knicholes/ah-my-groin-button/case/v1-200x130x110/preview-button-notch-detail.png

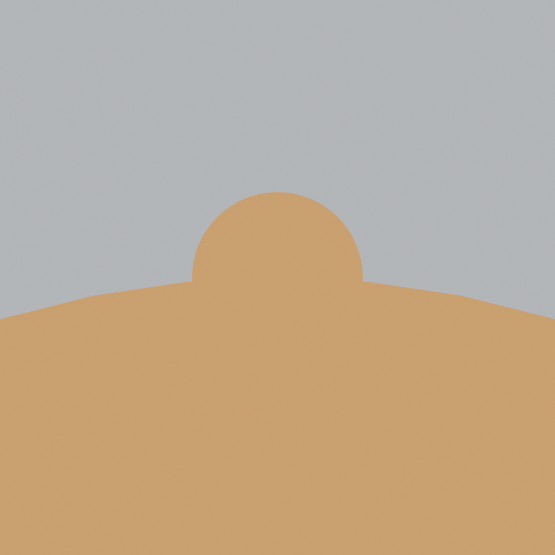
case/v1-200x130x110/preview-button-notch-detail.png
