knicholes/ah-my-groin-button/case/v1-200x130x110/preview-button-notches.png

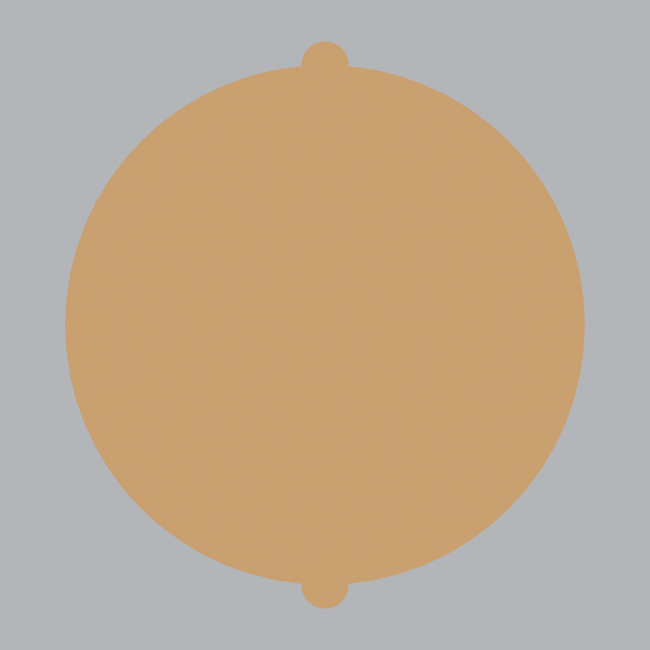
case/v1-200x130x110/preview-button-notches.png
