knicholes/ah-my-groin-button/case/v1-200x130x110/preview-tray-bottom.png

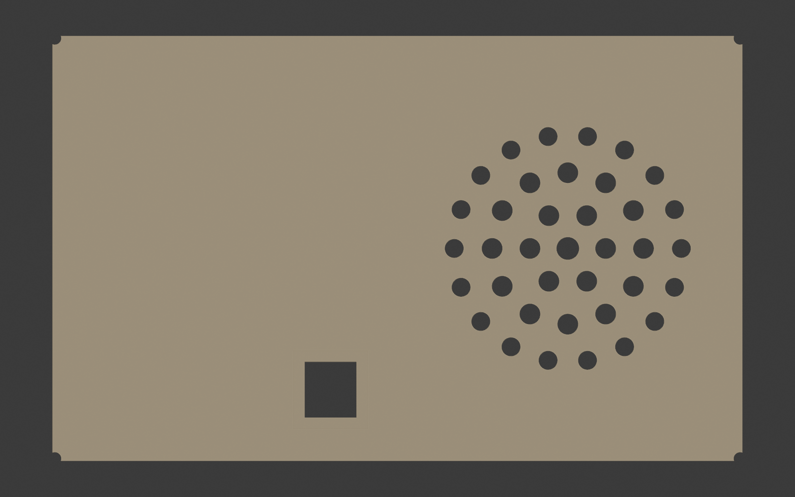
case/v1-200x130x110/preview-tray-bottom.png
