knicholes/ah-my-groin-button/case/v1-200x130x110/render-top.png

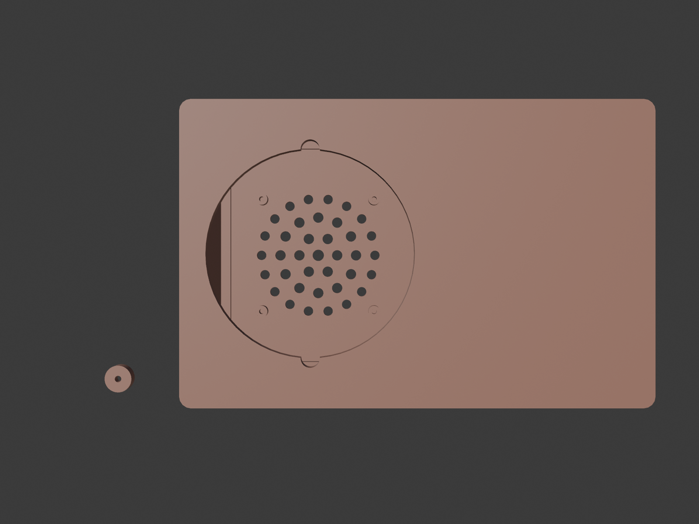
case/v1-200x130x110/render-top.png
