knicholes/ah-my-groin-button/case/v1-200x130x110/render-tray_top.png

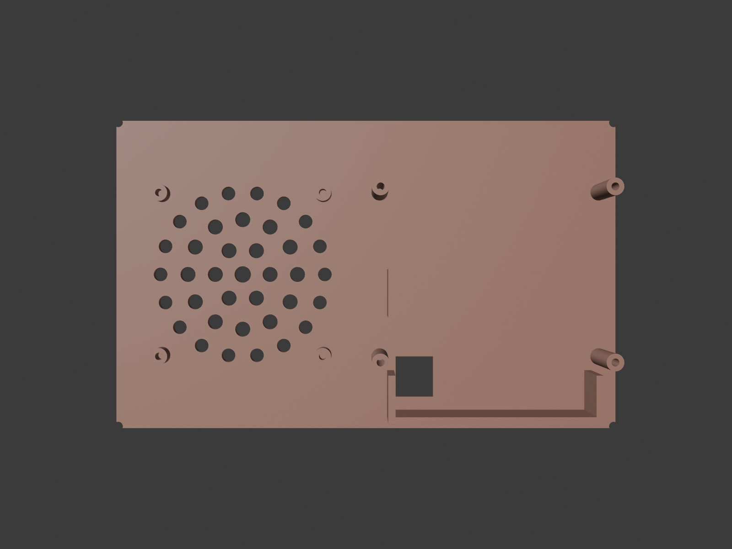
case/v1-200x130x110/render-tray_top.png
