knicholes/ah-my-groin-button/case/v2-120x120x140/preview-switch-window.png

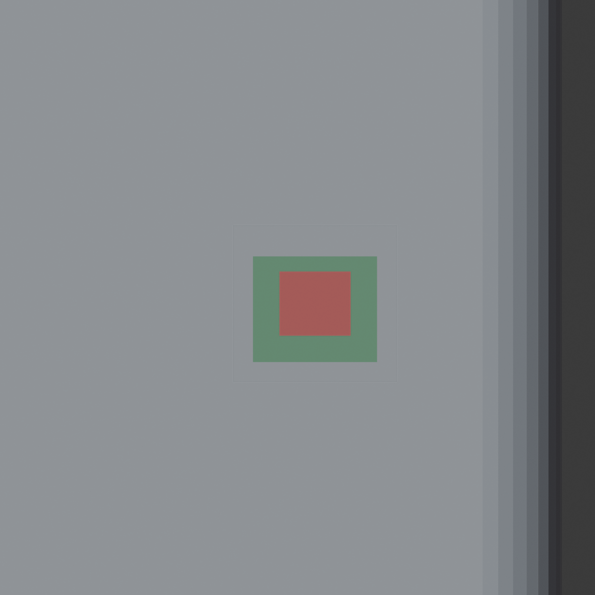
case/v2-120x120x140/preview-switch-window.png
