knicholes/ah-my-groin-button/kicad/fab/v3.2-top.png

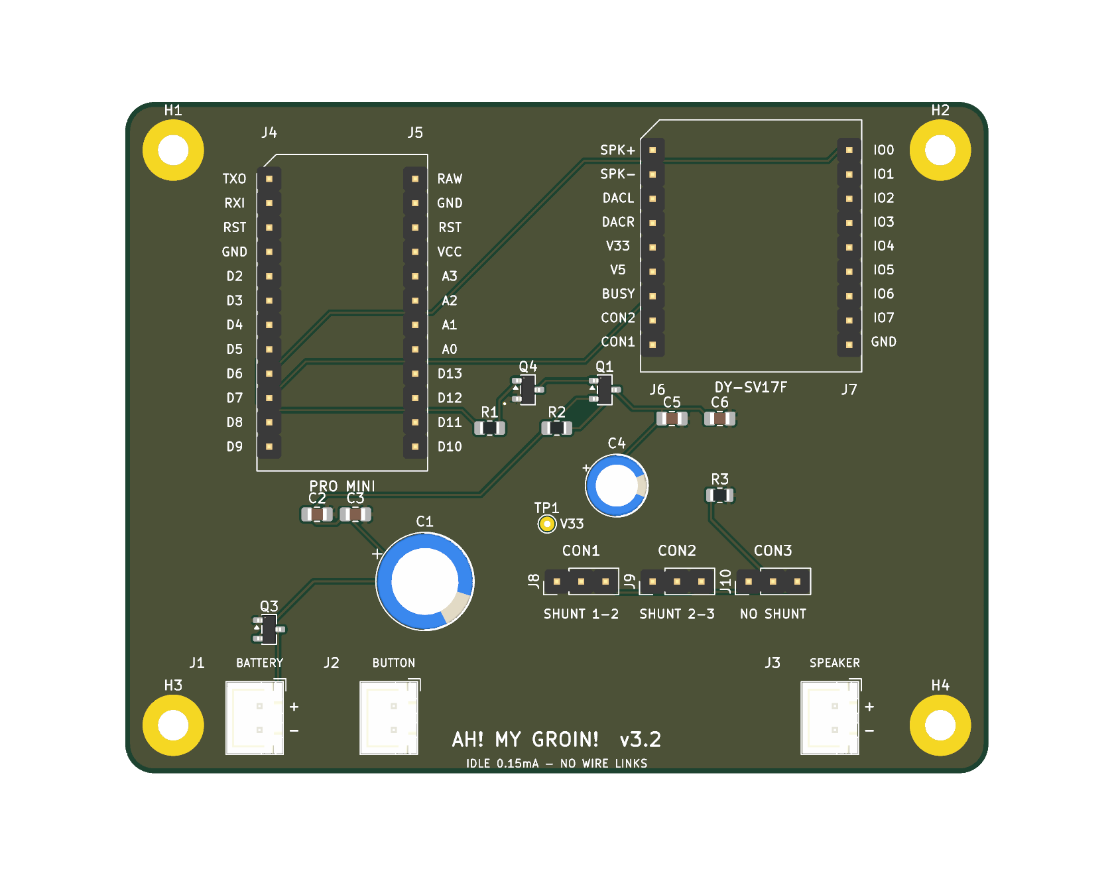
kicad/fab/v3.2-top.png
