knicholes/ah-my-groin-button/case/v1-200x130x110/preview-assembled.png

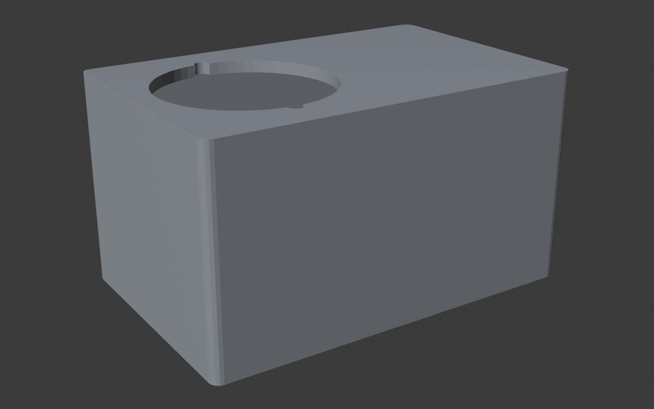
case/v1-200x130x110/preview-assembled.png
