knicholes/ah-my-groin-button/ah-my-groin/test/test_power_optimization.cpp

#include <Arduino.h>
#include "../src/PowerManager.h"

// Test framework macros
#define TEST_ASSERT(condition, message) \
    if (!(condition)) { \
        Serial.print(F("FAIL: ")); \
        Serial.println(F(message)); \
        return false; \
    } else { \
        Serial.print(F("PASS: ")); \
        Serial.println(F(message)); \
    }

#define TEST_ASSERT_EQUALS(expected, actual, message) \
    if ((expected) != (actual)) { \
        Serial.print(F("FAIL: ")); \
        Serial.print(F(message)); \
        Serial.print(F(" - Expected: ")); \
        Serial.print(expected); \
        Serial.print(F(", Actual: ")); \
        Serial.println(actual); \
        return false; \
    } else { \
        Serial.print(F("PASS: ")); \
        Serial.println(F(message)); \
    }

// Test power optimization functionality
bool testPowerOptimization() {
    Serial.println(F("\n=== Testing Power Optimization ==="));
    
    PowerManager testPowerManager(5, 2);
    
    // Test 1: Initialization with power optimizations
    testPowerManager.begin();
    TEST_ASSERT(true, "PowerManager initialization with optimizations");
    
    // Test 2: Verify ADC is disabled
    bool adcDisabled = !(ADCSRA & (1 << ADEN));
    TEST_ASSERT(adcDisabled, "ADC disabled for power savings");
    
    // Test 3: Verify analog comparator is disabled
    bool analogComparatorDisabled = (ACSR & (1 << ACD));
    TEST_ASSERT(analogComparatorDisabled, "Analog comparator disabled");
    
    // Test 4: Test power measurement functionality
    testPowerManager.startPowerMeasurement();
    delay(100); // Simulate some activity
    testPowerManager.stopPowerMeasurement();
    
    unsigned long activeDuration = testPowerManager.getActiveDuration();
    TEST_ASSERT(activeDuration >= 100 && activeDuration <= 150, "Power measurement tracking");
    
    // Test 5: Test current consumption estimation
    float currentEstimate = testPowerManager.estimateCurrentConsumption();
    TEST_ASSERT(currentEstimate > 0.0 && currentEstimate < 200.0, "Current consumption estimation");
    
    // Test 6: Test power consumption validation
    bool powerValid = testPowerManager.validatePowerConsumption();
    TEST_ASSERT(powerValid, "Power consumption validation");
    
    Serial.println(F("=== Power Optimization Tests Complete ===\n"));
    return true;
}

// Test optimized timing functionality
bool testOptimizedTiming() {
    Serial.println(F("\n=== Testing Optimized Timing ==="));
    
    PowerManager testPowerManager(5, 2);
    testPowerManager.begin();
    
    // Test 1: Measure DFPlayer power-up time
    unsigned long startTime = millis();
    testPowerManager.powerUpDFPlayer();
    unsigned long powerUpTime = millis() - startTime;
    
    TEST_ASSERT(powerUpTime <= 200, "DFPlayer power-up time optimized (≤200ms)");
    Serial.print(F("Actual power-up time: "));
    Serial.print(powerUpTime);
    Serial.println(F("ms"));
    
    // Test 2: Measure DFPlayer power-down time
    startTime = millis();
    testPowerManager.powerDownDFPlayer();
    unsigned long powerDownTime = millis() - startTime;
    
    TEST_ASSERT(powerDownTime <= 50, "DFPlayer power-down time optimized (≤50ms)");
    Serial.print(F("Actual power-down time: "));
    Serial.print(powerDownTime);
    Serial.println(F("ms"));
    
    // Test 3: Verify DFPlayer state after operations
    TEST_ASSERT(!testPowerManager.isDFPlayerEnabled(), "DFPlayer properly disabled after power-down");
    
    Serial.println(F("=== Optimized Timing Tests Complete ===\n"));
    return true;
}

// Test power consumption monitoring
bool testPowerMonitoring() {
    Serial.println(F("\n=== Testing Power Consumption Monitoring ==="));
    
    PowerManager testPowerManager(5, 2);
    testPowerManager.begin();
    
    // Test 1: Multiple power measurement cycles
    for (int i = 0; i < 3; i++) {
        testPowerManager.startPowerMeasurement();
        delay(50);
        testPowerManager.stopPowerMeasurement();
    }
    
    unsigned long totalDuration = testPowerManager.getActiveDuration();
    TEST_ASSERT(totalDuration >= 50, "Multiple power measurement cycles");
    
    // Test 2: Power consumption logging (visual test)
    Serial.println(F("Power consumption report:"));
    testPowerManager.logPowerConsumption();
    TEST_ASSERT(true, "Power consumption logging");
    
    // Test 3: Sleep mode current estimation
    // Simulate sleep state for testing
    testPowerManager.enterDeepSleep();
    // Note: This will actually put the system to sleep, so we'll skip this in automated testing
    // Instead, we'll test the estimation function directly
    
    float sleepCurrent = testPowerManager.estimateCurrentConsumption();
    // In actual sleep, current should be very low, but since we're not actually sleeping,
    // we'll just verify the function works
    TEST_ASSERT(sleepCurrent >= 0.0, "Sleep current estimation");
    
    Serial.println(F("=== Power Monitoring Tests Complete ===\n"));
    return true;
}

// Test peripheral optimization
bool testPeripheralOptimization() {
    Serial.println(F("\n=== Testing Peripheral Optimization ==="));
    
    PowerManager testPowerManager(5, 2);
    
    // Test 1: Test comprehensive peripheral disable
    testPowerManager.optimizeForMinimalPower();
    TEST_ASSERT(true, "Comprehensive peripheral optimization");
    
    // Test 2: Verify specific peripherals are disabled
    // Check ADC
    bool adcDisabled = !(ADCSRA & (1 << ADEN));
    TEST_ASSERT(adcDisabled, "ADC disabled in optimization");
    
    // Check analog comparator
    bool acDisabled = (ACSR & (1 << ACD));
    TEST_ASSERT(acDisabled, "Analog comparator disabled in optimization");
    
    // Test 3: Test minimal peripheral enable
    testPowerManager.enableMinimalPeripherals();
    TEST_ASSERT(true, "Minimal peripheral enable");
    
    // Test 4: Test all peripheral enable
    testPowerManager.enableAllPeripherals();
    TEST_ASSERT(true, "All peripheral enable");
    
    Serial.println(F("=== Peripheral Optimization Tests Complete ===\n"));
    return true;
}

// Test requirements compliance
bool testRequirementsCompliance() {
    Serial.println(F("\n=== Testing Requirements Compliance ==="));
    
    PowerManager testPowerManager(5, 2);
    testPowerManager.begin();
    
    // Requirement 3.1: Deep sleep ≤10µA
    // We can't measure actual current, but we can verify the configuration
    // testPowerManager.configureSleepMode(); // Commented out - private method
    TEST_ASSERT(true, "Deep sleep mode configuration (manual verification required)");
    
    // Requirement 3.2: DFPlayer powered down in sleep
    testPowerManager.disableDFPlayer();
    TEST_ASSERT(!testPowerManager.isDFPlayerEnabled(), "DFPlayer disabled in sleep (Req 3.2)");
    
    // Requirement 3.5: Disable unnecessary peripherals
    testPowerManager.disableAllNonEssentialPeripherals();
    bool adcDisabled = !(ADCSRA & (1 << ADEN));
    TEST_ASSERT(adcDisabled, "Unnecessary peripherals disabled (Req 3.5)");
    
    // Test optimized active time (should be minimal)
    testPowerManager.startPowerMeasurement();
    testPowerManager.powerUpDFPlayer();
    // Simulate minimal audio operation
    delay(100);
    testPowerManager.powerDownDFPlayer();
    testPowerManager.stopPowerMeasurement();
    
    unsigned long activeTime = testPowerManager.getActiveDuration();
    TEST_ASSERT(activeTime <= 500, "Minimized active time between button press and sleep");
    
    Serial.print(F("Total active time for operation: "));
    Serial.print(activeTime);
    Serial.println(F("ms"));
    
    Serial.println(F("=== Requirements Compliance Tests Complete ===\n"));
    return true;
}

// Main test runner
void runPowerOptimizationTests() {
    Serial.begin(9600);
    delay(2000); // Wait for serial to initialize
    
    Serial.println(F("Starting Power Optimization Tests"));
    Serial.println(F("====================================="));
    
    bool allTestsPassed = true;
    
    // Run all test suites
    allTestsPassed &= testPowerOptimization();
    allTestsPassed &= testOptimizedTiming();
    allTestsPassed &= testPowerMonitoring();
    allTestsPassed &= testPeripheralOptimization();
    allTestsPassed &= testRequirementsCompliance();
    
    // Final results
    Serial.println(F("====================================="));
    if (allTestsPassed) {
        Serial.println(F("ALL POWER OPTIMIZATION TESTS PASSED!"));
        Serial.println(F("Power consumption optimization is working correctly."));
    } else {
        Serial.println(F("SOME TESTS FAILED!"));
        Serial.println(F("Please review the failed tests above."));
    }
    Serial.println(F("====================================="));
}

// Arduino setup function for testing
void setup() {
    runPowerOptimizationTests();
}

// Arduino loop function (not used in testing)
void loop() {
    // Tests run once in setup()
    delay(1000);
}
