knicholes/ah-my-groin-button/ah-my-groin/test/test_button_handler.cpp

/*
 * ButtonHandler Test Suite
 * 
 * Tests for the ButtonHandler class functionality including:
 * - Interrupt-based input detection
 * - Software debouncing
 * - Button state management and change detection
 * 
 * Requirements tested: 4.1, 4.2, 4.3, 4.4
 */

#include <Arduino.h>
#include <unity.h>
#include "../src/ButtonHandler.h"

// Test configuration
const int TEST_BUTTON_PIN = 2;
const unsigned long TEST_DEBOUNCE_DELAY = 50;

// Test helper functions
void simulateButtonPress() {
    // Simulate button press by setting pin LOW
    pinMode(TEST_BUTTON_PIN, OUTPUT);
    digitalWrite(TEST_BUTTON_PIN, LOW);
    delay(10);
}

void simulateButtonRelease() {
    // Simulate button release by setting pin HIGH (pull-up)
    pinMode(TEST_BUTTON_PIN, INPUT_PULLUP);
    delay(10);
}

void simulateButtonBounce() {
    // Simulate mechanical bouncing
    for (int i = 0; i < 5; i++) {
        digitalWrite(TEST_BUTTON_PIN, LOW);
        delay(2);
        digitalWrite(TEST_BUTTON_PIN, HIGH);
        delay(2);
    }
    digitalWrite(TEST_BUTTON_PIN, LOW); // Final stable state
}

void setUp(void) {
    // Initialize ButtonHandler for testing
    buttonHandler.begin();
    delay(100);
}

void tearDown(void) {
    // Reset button state after each test
    buttonHandler.reset();
    simulateButtonRelease();
    delay(100);
}

// Test 1: Basic initialization and setup
void test_button_handler_initialization() {
    ButtonHandler testHandler(TEST_BUTTON_PIN, TEST_DEBOUNCE_DELAY);
    testHandler.begin();
    
    // Verify initial state
    TEST_ASSERT_FALSE(testHandler.isPressed());
    TEST_ASSERT_FALSE(testHandler.wasPressed());
    TEST_ASSERT_FALSE(testHandler.wasReleased());
    TEST_ASSERT_FALSE(testHandler.stateChanged());
    TEST_ASSERT_EQUAL(TEST_DEBOUNCE_DELAY, testHandler.getDebounceDelay());
    TEST_ASSERT_EQUAL(0, testHandler.getPressCount());
}

// Test 2: Button press detection (Requirement 4.1)
void test_button_press_detection() {
    // Ensure button starts in released state
    simulateButtonRelease();
    buttonHandler.update();
    TEST_ASSERT_FALSE(buttonHandler.isPressed());
    
    // Simulate button press
    simulateButtonPress();
    buttonHandler.update();
    delay(TEST_DEBOUNCE_DELAY + 10); // Wait for debounce
    buttonHandler.update();
    
    // Verify button press is detected
    TEST_ASSERT_TRUE(buttonHandler.isPressed());
    TEST_ASSERT_TRUE(buttonHandler.wasPressed());
    TEST_ASSERT_TRUE(buttonHandler.stateChanged());
    TEST_ASSERT_EQUAL(1, buttonHandler.getPressCount());
}

// Test 3: Button release detection
void test_button_release_detection() {
    // Start with button pressed
    simulateButtonPress();
    buttonHandler.update();
    delay(TEST_DEBOUNCE_DELAY + 10);
    buttonHandler.update();
    
    // Clear the wasPressed flag
    buttonHandler.wasPressed();
    buttonHandler.stateChanged();
    
    // Simulate button release
    simulateButtonRelease();
    buttonHandler.update();
    delay(TEST_DEBOUNCE_DELAY + 10);
    buttonHandler.update();
    
    // Verify button release is detected
    TEST_ASSERT_FALSE(buttonHandler.isPressed());
    TEST_ASSERT_TRUE(buttonHandler.wasReleased());
    TEST_ASSERT_TRUE(buttonHandler.stateChanged());
}

// Test 4: Software debouncing prevents multiple triggers (Requirement 4.2)
void test_debouncing_prevents_multiple_triggers() {
    unsigned long initialPressCount = buttonHandler.getPressCount();
    
    // Simulate bouncing button press
    pinMode(TEST_BUTTON_PIN, OUTPUT);
    simulateButtonBounce();
    
    // Update multiple times during bounce period
    for (int i = 0; i < 10; i++) {
        buttonHandler.update();
        delay(5);
    }
    
    // Wait for debounce period to complete
    delay(TEST_DEBOUNCE_DELAY + 10);
    buttonHandler.update();
    
    // Verify only one press is registered despite bouncing
    TEST_ASSERT_EQUAL(initialPressCount + 1, buttonHandler.getPressCount());
    TEST_ASSERT_TRUE(buttonHandler.isPressed());
}

// Test 5: Single press doesn't repeat when held (Requirement 4.3)
void test_held_button_single_trigger() {
    // Press and hold button
    simulateButtonPress();
    buttonHandler.update();
    delay(TEST_DEBOUNCE_DELAY + 10);
    buttonHandler.update();
    
    unsigned long pressCountAfterPress = buttonHandler.getPressCount();
    bool wasPressed = buttonHandler.wasPressed(); // This should clear the flag
    
    // Continue holding button and updating
    for (int i = 0; i < 20; i++) {
        buttonHandler.update();
        delay(10);
    }
    
    // Verify no additional presses are registered
    TEST_ASSERT_EQUAL(pressCountAfterPress, buttonHandler.getPressCount());
    TEST_ASSERT_FALSE(buttonHandler.wasPressed()); // Should be false after first read
    TEST_ASSERT_TRUE(buttonHandler.isPressed()); // Should still be pressed
}

// Test 6: Button state change detection
void test_state_change_detection() {
    // Start with button released
    simulateButtonRelease();
    buttonHandler.update();
    delay(TEST_DEBOUNCE_DELAY + 10);
    buttonHandler.update();
    
    // Clear any initial state change
    buttonHandler.stateChanged();
    
    // Press button
    simulateButtonPress();
    buttonHandler.update();
    delay(TEST_DEBOUNCE_DELAY + 10);
    buttonHandler.update();
    
    // Verify state change is detected
    TEST_ASSERT_TRUE(buttonHandler.stateChanged());
    
    // Clear state change flag
    buttonHandler.stateChanged();
    
    // Update without changing button state
    buttonHandler.update();
    
    // Verify no state change when button state is stable
    TEST_ASSERT_FALSE(buttonHandler.stateChanged());
}

// Test 7: Interrupt-based input (Requirement 4.4)
void test_interrupt_setup() {
    // This test verifies that interrupt setup doesn't crash
    // Actual interrupt testing requires hardware simulation
    buttonHandler.setupInterrupt();
    buttonHandler.enableInterrupt();
    
    // Verify interrupt can be disabled and re-enabled
    buttonHandler.disableInterrupt();
    buttonHandler.enableInterrupt();
    
    // Test passes if no exceptions are thrown
    TEST_ASSERT_TRUE(true);
}

// Test 8: Debounce delay configuration
void test_debounce_delay_configuration() {
    const unsigned long newDelay = 100;
    
    buttonHandler.setDebounceDelay(newDelay);
    TEST_ASSERT_EQUAL(newDelay, buttonHandler.getDebounceDelay());
    
    // Test that new delay is actually used
    simulateButtonPress();
    buttonHandler.update();
    delay(TEST_DEBOUNCE_DELAY + 10); // Old delay
    buttonHandler.update();
    
    // Should not be debounced yet with new longer delay
    // Note: This test may be timing-sensitive
    TEST_ASSERT_TRUE(buttonHandler.isPressed() || !buttonHandler.isPressed()); // Either state is valid during debounce
}

// Test 9: Reset functionality
void test_reset_functionality() {
    // Press button and accumulate some state
    simulateButtonPress();
    buttonHandler.update();
    delay(TEST_DEBOUNCE_DELAY + 10);
    buttonHandler.update();
    
    unsigned long pressCount = buttonHandler.getPressCount();
    TEST_ASSERT_GREATER_THAN(0, pressCount);
    
    // Reset the handler
    buttonHandler.reset();
    
    // Verify state is reset
    TEST_ASSERT_EQUAL(0, buttonHandler.getPressCount());
    TEST_ASSERT_FALSE(buttonHandler.wasPressed());
    TEST_ASSERT_FALSE(buttonHandler.wasReleased());
    TEST_ASSERT_FALSE(buttonHandler.stateChanged());
}

// Test 10: Timing information accuracy
void test_timing_information() {
    unsigned long startTime = millis();
    
    // Press button
    simulateButtonPress();
    buttonHandler.update();
    delay(TEST_DEBOUNCE_DELAY + 10);
    buttonHandler.update();
    
    unsigned long pressTime = buttonHandler.getLastPressTime();
    TEST_ASSERT_GREATER_OR_EQUAL(startTime, pressTime);
    TEST_ASSERT_LESS_THAN(startTime + 200, pressTime); // Should be within 200ms
    
    // Release button
    delay(50);
    simulateButtonRelease();
    buttonHandler.update();
    delay(TEST_DEBOUNCE_DELAY + 10);
    buttonHandler.update();
    
    unsigned long releaseTime = buttonHandler.getLastReleaseTime();
    TEST_ASSERT_GREATER_THAN(pressTime, releaseTime);
}

void setup() {
    delay(2000); // Wait for serial monitor
    
    UNITY_BEGIN();
    
    // Run all tests
    RUN_TEST(test_button_handler_initialization);
    RUN_TEST(test_button_press_detection);
    RUN_TEST(test_button_release_detection);
    RUN_TEST(test_debouncing_prevents_multiple_triggers);
    RUN_TEST(test_held_button_single_trigger);
    RUN_TEST(test_state_change_detection);
    RUN_TEST(test_interrupt_setup);
    RUN_TEST(test_debounce_delay_configuration);
    RUN_TEST(test_reset_functionality);
    RUN_TEST(test_timing_information);
    
    UNITY_END();
}

void loop() {
    // Empty - tests run once in setup()
}
