knicholes/ah-my-groin-button/ah-my-groin/test/compile_test_system_state_machine.cpp

/*
 * Compilation Test for System State Machine Implementation
 * 
 * This file tests that the state machine implementation compiles correctly
 * and all required components are properly integrated.
 */

#include <Arduino.h>

// Test that all required headers can be included
#include "../src/SystemController.h"
#include "../src/PowerManager.h"
#include "../src/AudioController.h"
#include "../src/ButtonHandler.h"

// Test that SystemState enum is properly defined
void testSystemStateEnum() {
    SystemState states[] = {
        DEEP_SLEEP,
        WAKING_UP,
        POWERING_UP,
        PLAYING,
        POWERING_DOWN,
        ERROR_STATE
    };
    
    // Verify all states are accessible
    for (int i = 0; i < 6; i++) {
        SystemState state = states[i];
        (void)state; // Suppress unused variable warning
    }
}

// Test that SystemController interface is complete
void testSystemControllerInterface() {
    // Create mock components
    PowerManager powerMgr(5);
    AudioController audioCtrl(3, 4);
    ButtonHandler buttonHdlr(2);
    SystemController sysCtrl(powerMgr, audioCtrl, buttonHdlr);
    
    // Test all required methods exist and can be called
    bool result;
    
    // Initialization
    result = sysCtrl.begin();
    (void)result;
    
    // Main operations
    sysCtrl.handleButtonPress();
    sysCtrl.enterSleepMode();
    
    // State management
    SystemState state = sysCtrl.getCurrentState();
    (void)state;
    
    result = sysCtrl.isSystemReady();
    (void)result;
    
    // Error handling
    result = sysCtrl.hasError();
    (void)result;
    
    sysCtrl.clearError();
    
    const char* error = sysCtrl.getLastError();
    (void)error;
    
    // Power management integration
    result = sysCtrl.powerUpAudioSystem();
    (void)result;
    
    result = sysCtrl.powerDownAudioSystem();
    (void)result;
    
    result = sysCtrl.initializeAudioSystem();
    (void)result;
    
    // Timing and sequencing
    result = sysCtrl.waitForSystemReady(3000);
    (void)result;
    
    sysCtrl.executeStartupSequence();
    sysCtrl.executeShutdownSequence();
    
    // Error recovery
    result = sysCtrl.recoverFromError();
    (void)result;
    
    sysCtrl.resetSystem();
    
    // Status information
    unsigned long time = sysCtrl.getLastOperationTime();
    (void)time;
    
    time = sysCtrl.getTotalOperationTime();
    (void)time;
}

// Test that main Arduino integration compiles
void testMainIntegration() {
    // Test that all required components can be instantiated
    PowerManager powerManager(5);
    AudioController audioController(3, 4);
    ButtonHandler buttonHandler(2);
    SystemController systemController(powerManager, audioController, buttonHandler);
    
    // Test that all components can be initialized
    bool result;
    result = powerManager.begin();
    (void)result;
    
    result = audioController.begin();
    (void)result;
    
    result = buttonHandler.begin();
    (void)result;
    
    result = systemController.begin();
    (void)result;
    
    // Test state machine operations
    systemController.handleButtonPress();
    systemController.enterSleepMode();
    
    SystemState currentState = systemController.getCurrentState();
    (void)currentState;
}

void setup() {
    Serial.begin(9600);
    Serial.println(F("System State Machine Compilation Test"));
    
    // Run compilation tests
    testSystemStateEnum();
    testSystemControllerInterface();
    testMainIntegration();
    
    Serial.println(F("All compilation tests passed!"));
    Serial.println(F("State machine implementation compiles successfully."));
}

void loop() {
    // Test complete
    delay(1000);
}
