knicholes/ah-my-groin-button/ah-my-groin/test/compile_test_audio_controller.cpp

/*
 * Compilation Test for AudioController
 * 
 * This file tests that the AudioController compiles correctly
 * and validates the trigger-based audio implementation.
 */

#include <Arduino.h>
#include <SoftwareSerial.h>
#include "../src/AudioController.h"

// Test that AudioController can be instantiated
SoftwareSerial testSerial(4, 3);
AudioController testController(testSerial, 15);

void setup() {
    Serial.begin(9600);
    Serial.println(F("AudioController compilation test"));
    
    // Test basic interface
    bool initialized = testController.isInitialized();
    bool playing = testController.isPlaying();
    bool hasError = testController.hasError();
    int volume = testController.getVolume();
    
    Serial.println(F("✓ AudioController interface accessible"));
    Serial.println(F("✓ Trigger-based audio implementation compiled successfully"));
    Serial.println(F("✓ All required methods available"));
    
    Serial.print(F("Initial state - Initialized: "));
    Serial.print(initialized ? "true" : "false");
    Serial.print(F(", Playing: "));
    Serial.print(playing ? "true" : "false");
    Serial.print(F(", Volume: "));
    Serial.println(volume);
    
    Serial.println(F("Compilation test complete"));
}

void loop() {
    // Nothing to do
}
